Technofrikus/Boston-Case/Photos/DSCF7717 1.jpg

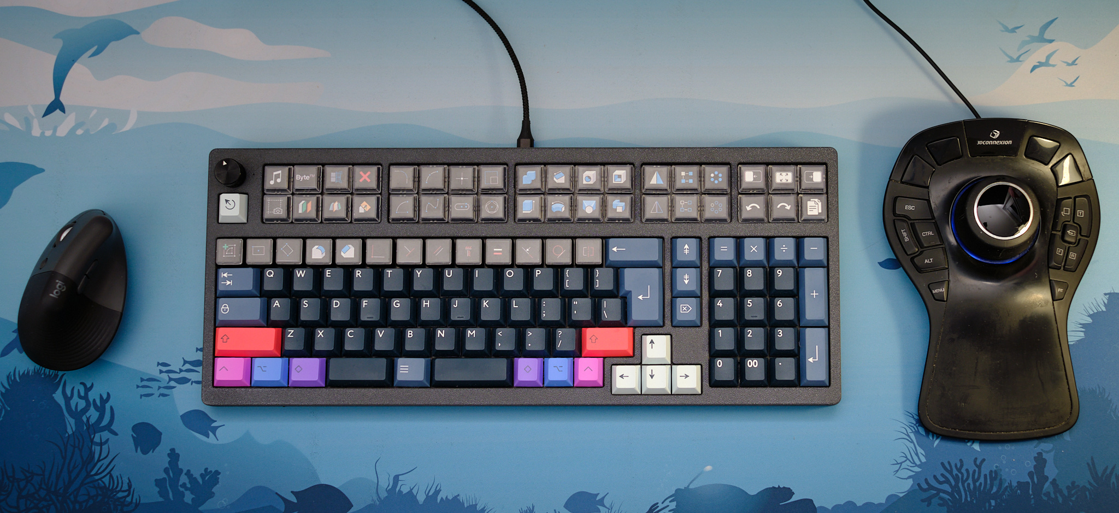
Photos/DSCF7717 1.jpg
