Technofrikus/Boston-Case/Photos/DSCF7732 1.jpg

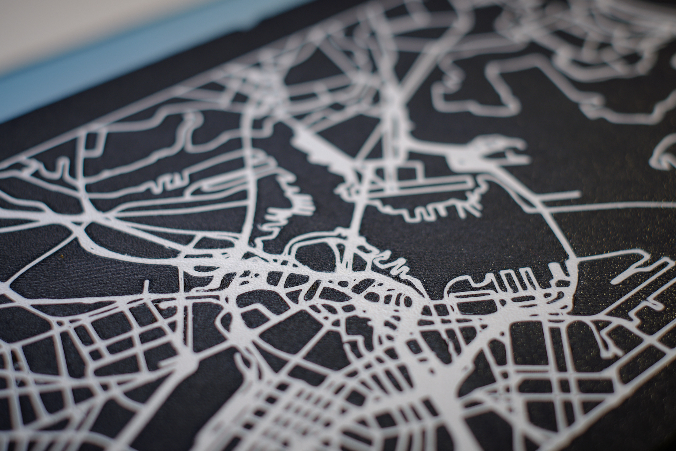
Photos/DSCF7732 1.jpg
